wpwrak/idbg/web/glued.jpg

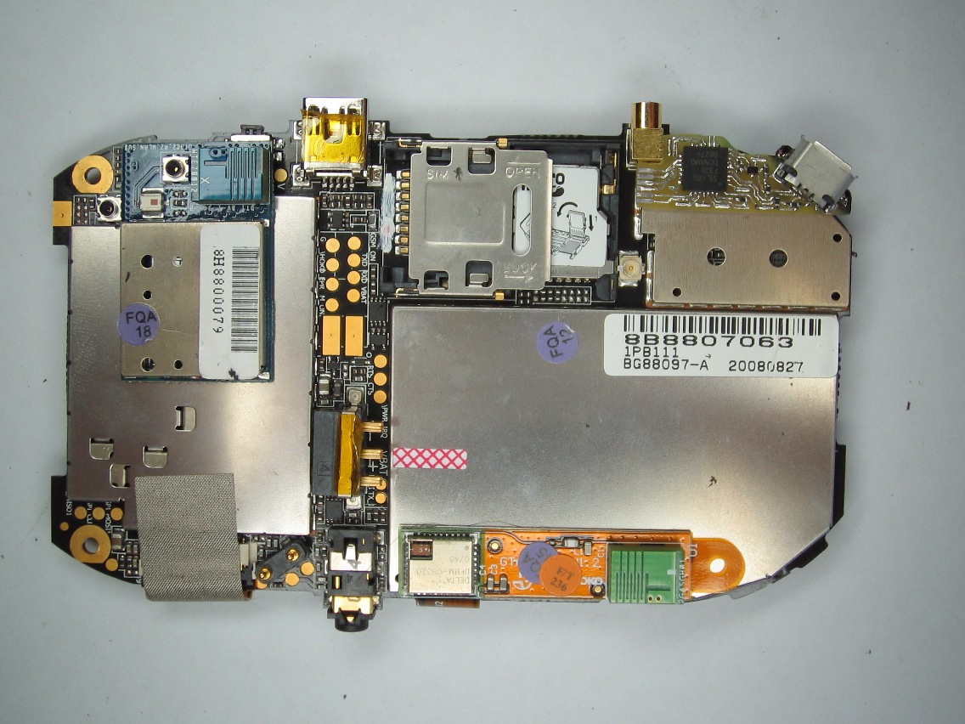
web/glued.jpg
