wpwrak/idbg/web/hole-before.jpg

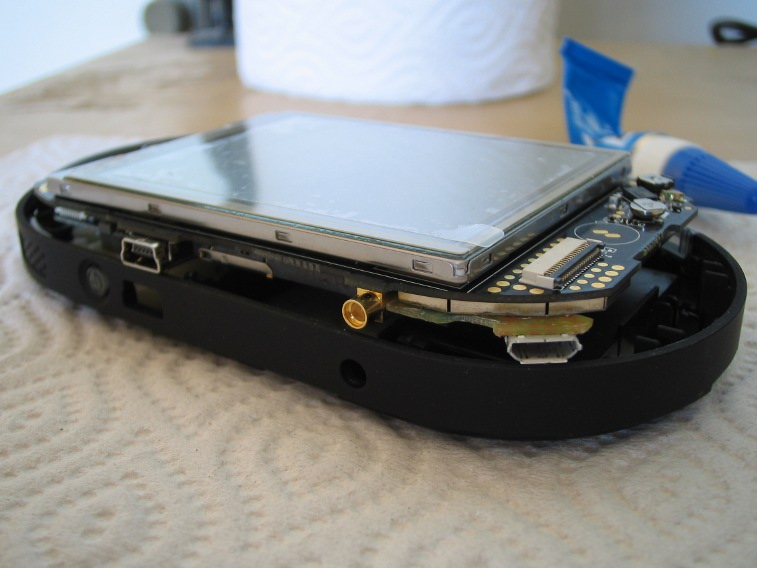
web/hole-before.jpg
