wpwrak/idbg/web/hole-done.jpg

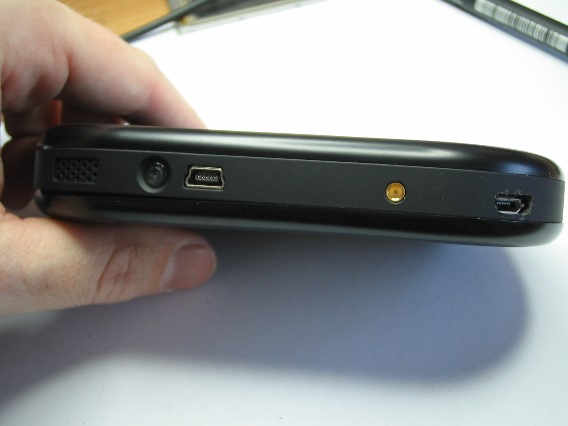
web/hole-done.jpg
