wpwrak/idbg/web/hole-zoom.jpg

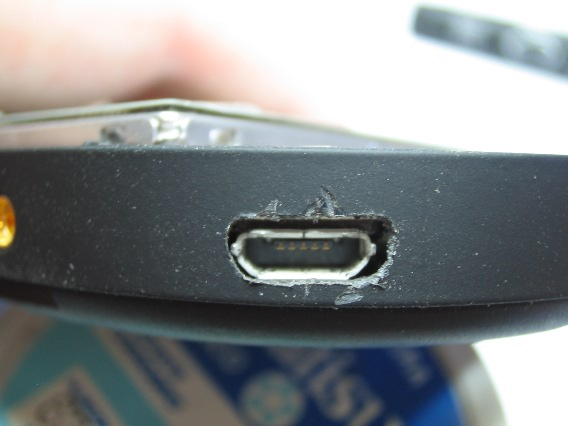
web/hole-zoom.jpg
