wpwrak/idbg/web/idbg-coexistence.jpg

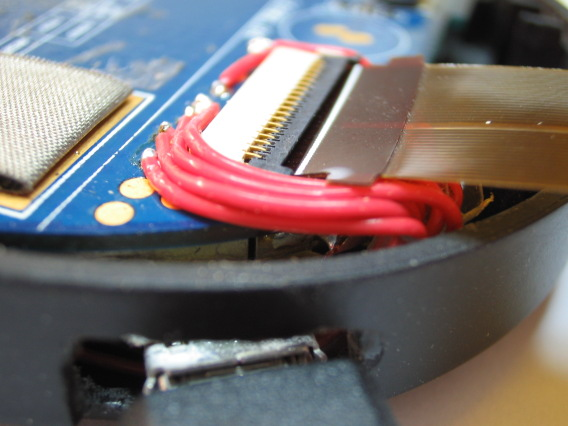
web/idbg-coexistence.jpg
