wpwrak/idbg/web/idbg-ipl.jpg

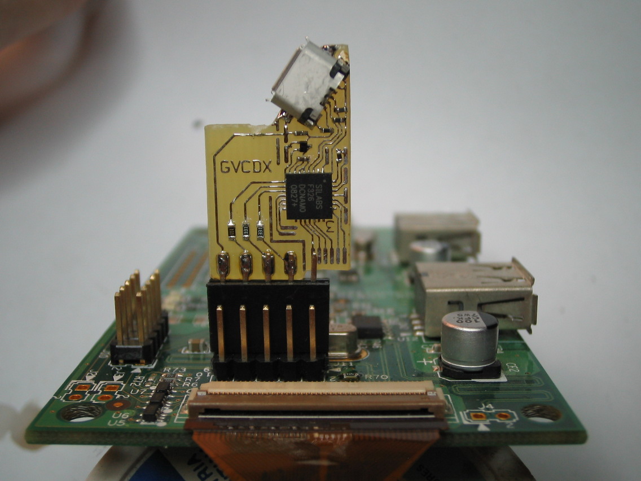
web/idbg-ipl.jpg
