wpwrak/idbg/web/idbg-top.jpg

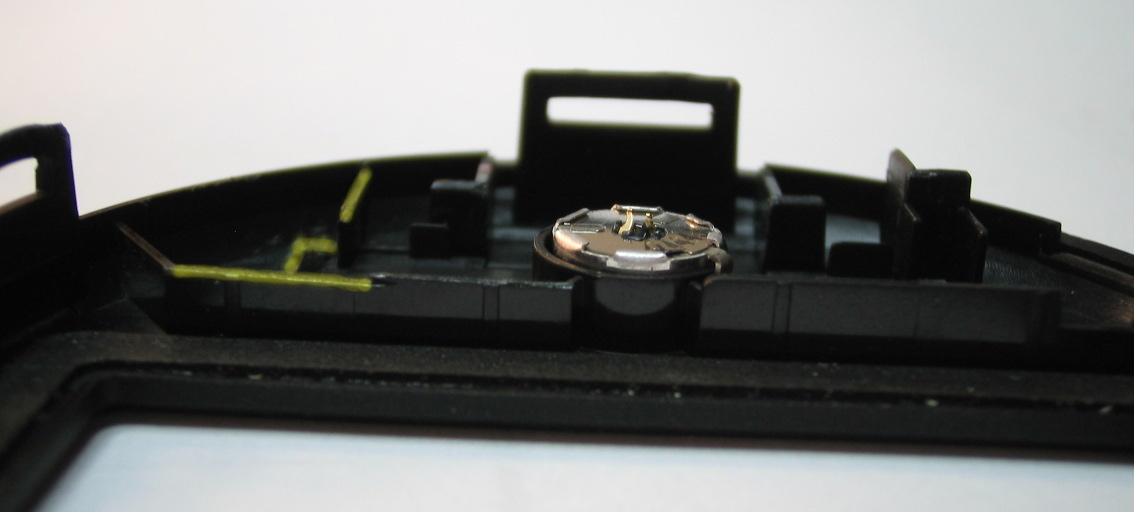
web/idbg-top.jpg
