wpwrak/idbg/web/idbg-wired.jpg

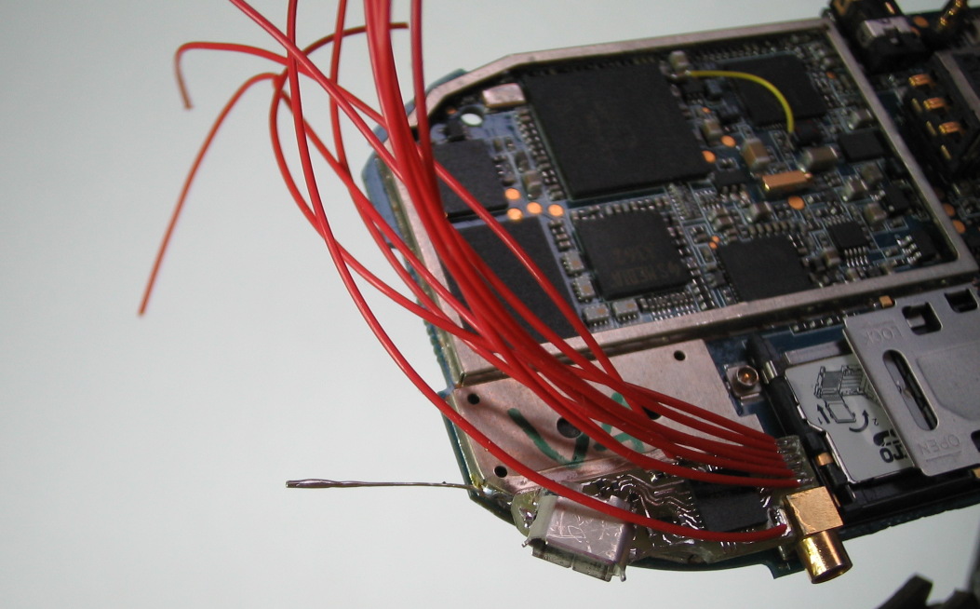
web/idbg-wired.jpg
