wpwrak/idbg/web/idbg-wires.jpg

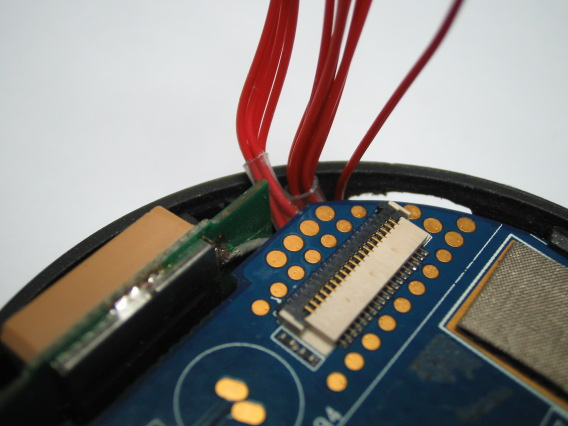
web/idbg-wires.jpg
