wpwrak/idbg/web/works.jpg

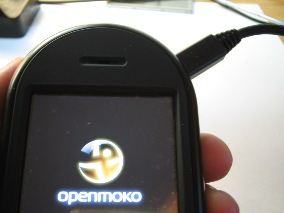
web/works.jpg
