wpwrak/idbg/web/ww-connected.jpg

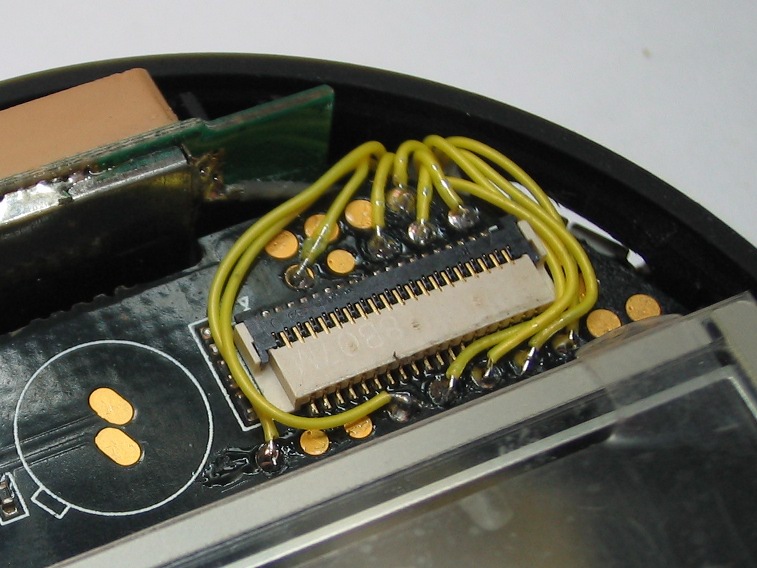
web/ww-connected.jpg
