wpwrak/idbg/web/ww-gnd.jpg

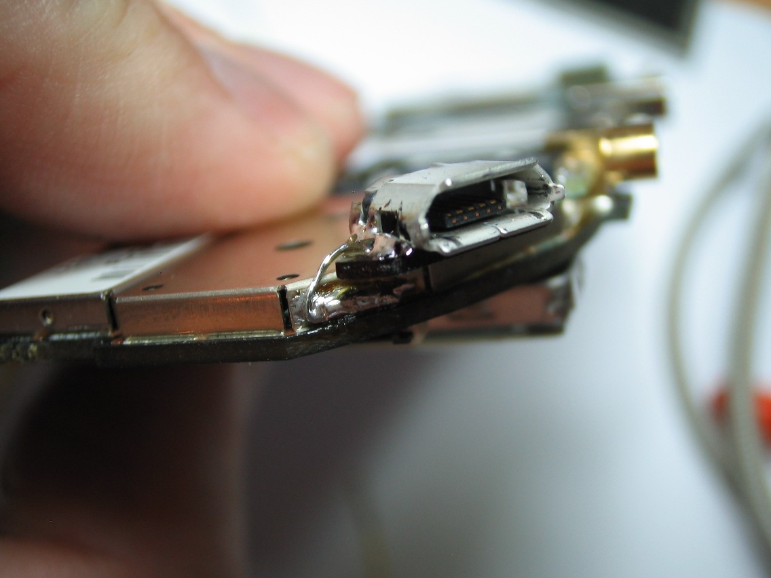
web/ww-gnd.jpg
