wpwrak/idbg/web/ww-wired.jpg

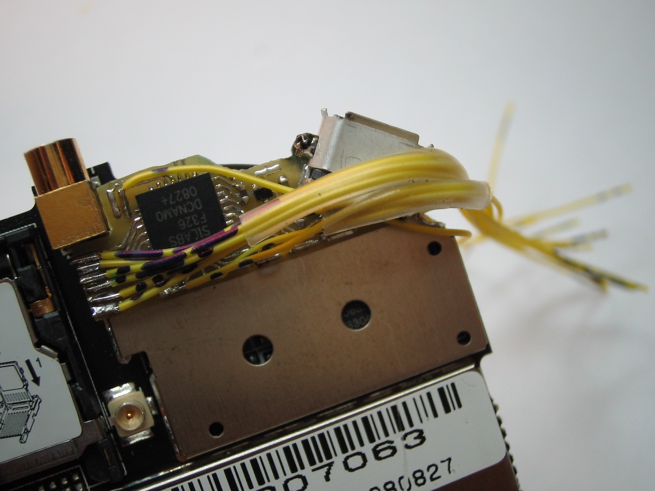
web/ww-wired.jpg
