wpwrak/idbg/hw/idbg-ben.sch

## KiCad design hw/idbg-ben.sch (2010-08-10, an earlier design)

Schematic: idbg-ben.sch

Parts:
C1: 1uF
C2: 100nF
P1: USB B
P2, P3, P4, P5, P6, P7, P8: CONN_1
R1, R2: 0
U1: C8051F326
VR1, VR2, VR3: 5V6
