wpwrak/idbg/hw/idbg.sch

## KiCad design hw/idbg.sch (2009-01-06)

Schematic: idbg.sch

Parts:
C1: 1uF
C2: 100nF
D1: DDSCHCC
P1: USB B
P2, P3, P5, P6, P7, P8, P9, P10, P11, P12, P13, P14, P15, P16, P17, P18, P19, P21, P22: CONN_1
R1: 100
R2, R3: 330
R4: 100k
U1: C8051F326
VR1, VR2, VR3: 5V6

Notes on the sheet:
IPL board
