wpwrak/idbg/fw/idbg/descr.c

/*
 * idbg/descr.c - USB descriptors
 *
 * Written 2008-2010 by Werner Almesberger
 * Copyright 2008-2010 Werner Almesberger
 *
 * This program is free software; you can redistribute it and/or modify
 * it under the terms of the GNU General Public License as published by
 * the Free Software Foundation; either version 2 of the License, or
 * (at your option) any later version.
 */


#include "usb.h"
#include "idbg/usb-ids.h"


/*
 * Device descriptor
 */

const uint8_t device_descriptor[18] = {
	18,			/* bLength */
	USB_DT_DEVICE,		/* bDescriptorType */
	LE(0x200),		/* bcdUSB */
	USB_CLASS_VENDOR_SPEC,	/* bDeviceClass */
	0x00,			/* bDeviceSubClass */
	0x00,			/* bDeviceProtocol */
	EP0_SIZE,		/* bMaxPacketSize */
	LE(USB_VENDOR),		/* idVendor */
	LE(USB_PRODUCT_IDBG),	/* idProduct */
	LE(0x0001),		/* bcdDevice */
	0,			/* iManufacturer */
	0,			/* iProduct */
	0,			/* iSerialNumber */
	1			/* bNumConfigurations */
};


/*
 * Our configuration
 *
 * While in DFU mode, we're always bus-powered.
 */

const uint8_t config_descriptor[] = {
	9,			/* bLength */
	USB_DT_CONFIG,		/* bDescriptorType */
	LE(9+9+7+7),		/* wTotalLength */
	1,			/* bNumInterfaces */
	1,			/* bConfigurationValue (> 0 !) */
	0,			/* iConfiguration */
//	USB_ATTR_SELF_POWERED | USB_ATTR_BUS_POWERED,
	USB_ATTR_BUS_POWERED,	/* bmAttributes */
	15,			/* bMaxPower */

	/* Interface #0 */

	9,			/* bLength */
	USB_DT_INTERFACE,	/* bDescriptorType */
	0,			/* bInterfaceNumber */
	0,			/* bAlternateSetting */
	2,			/* bNumEndpoints */
	USB_CLASS_VENDOR_SPEC,	/* bInterfaceClass */
	0,			/* bInterfaceSubClass */
	0,			/* bInterfaceProtocol */
	0,			/* iInterface */

	/* EP OUT */

	7,			/* bLength */
	USB_DT_ENDPOINT,	/* bDescriptorType */
	0x01,			/* bEndPointAddress */
	0x02,			/* bmAttributes (bulk) */
	LE(EP1_SIZE),		/* wMaxPacketSize */
	0,			/* bInterval */

	/* EP IN */

	7,			/* bLength */
	USB_DT_ENDPOINT,	/* bDescriptorType */
	0x81,			/* bEndPointAddress */
	0x02,			/* bmAttributes (bulk) */
	LE(EP1_SIZE),		/* wMaxPacketSize */
	0,			/* bInterval */

};
